LucasZuniga/Proyecto_IRB/software/extras/wifi_conect.py

import time
import network
import urequests as requests

ssid = 'Lucas'
password = '1234567890'

wlan = network.WLAN(network.STA_IF)

#function to connect to Wi-Fi network
def cnctWifi():
    
    wlan.active(True)
    wlan.connect(ssid, password)
    
    # Wait for connection to establish
    max_wait = 10
    while max_wait > 0:
        if wlan.status() < 0 or wlan.status() >= 3:
                break
        max_wait -= 1
        print('waiting for connection...')
        time.sleep(1)
    
    # Manage connection errors
    if wlan.status() != 3:
        print('Network Connection has failed')
    else:
        print('connected')
        status = wlan.ifconfig()
        print( 'ip = ' + status[0] )

#function to send http get request
def getData():
    try:
        data=requests.get("http://api.open-notify.org/iss-now.json")
        location=data.json()
        print("ISS latitude={}".format(location['iss_position']['latitude']))
        print("ISS longitude={}".format(location['iss_position']['longitude']))
        data.close()

    except:
        print("could not connect (status =" + str(wlan.status()) + ")")

cnctWifi() 
   
while True:
    try:
        if wlan.isconnected():
            print("sending get request...")
            getData()
        else:
            print("attempting to reconnect...")
            wlan.disconnect()
            cnctWifi()
        time.sleep(1)
    except KeyboardInterrupt:
        break
    
